brev-dev/another_esp8266_sensor_board/datasheets/microUSB_socket_2pin.jpg

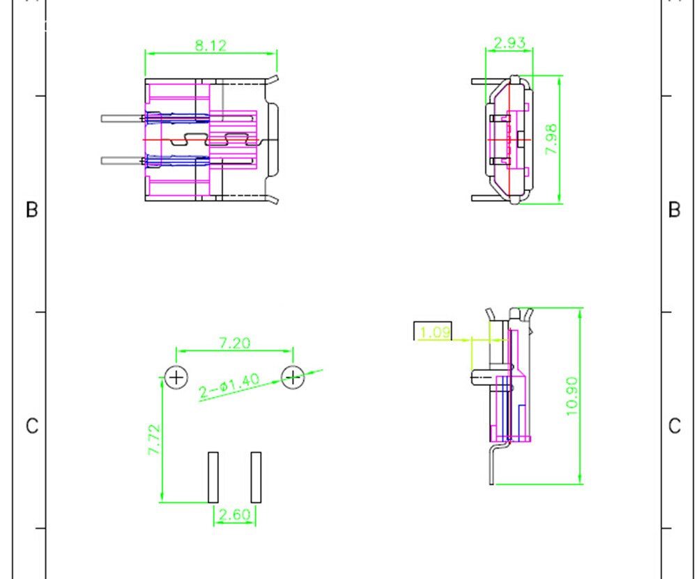
datasheets/microUSB_socket_2pin.jpg
