brev-dev/another_esp8266_sensor_board/datasheets/usbc_socket_6pin.webp

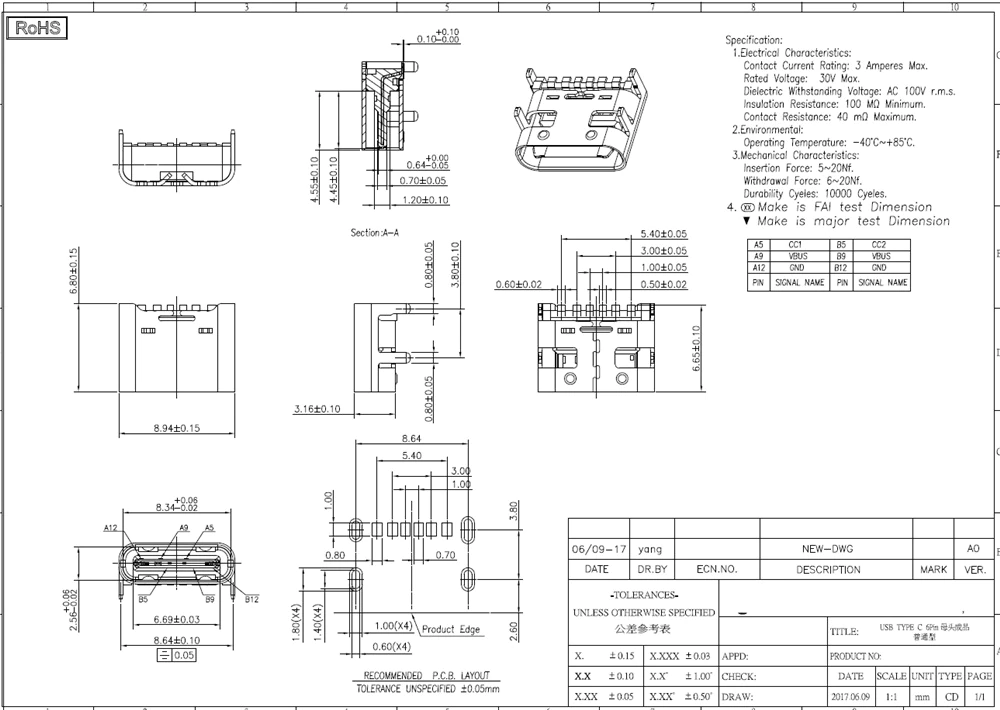
datasheets/usbc_socket_6pin.webp
