brev-dev/another_esp8266_sensor_board/images/antenna_bottom.jpg

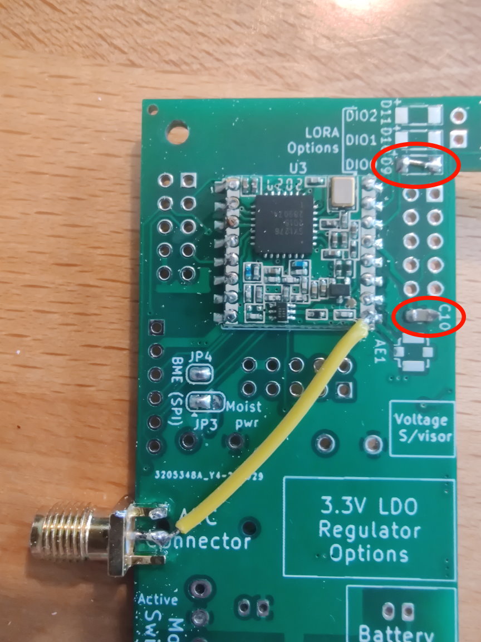
images/antenna_bottom.jpg
