brev-dev/another_esp8266_sensor_board/images/audio_socket_mod.jpg

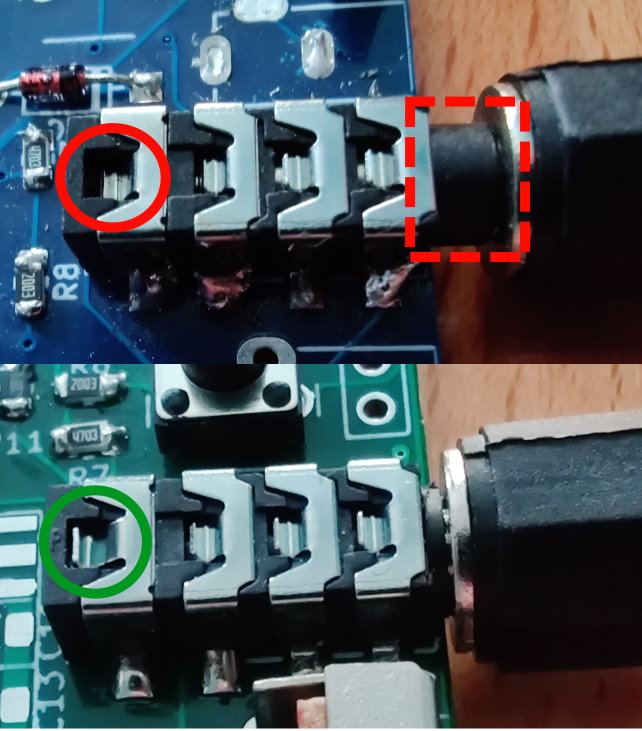
images/audio_socket_mod.jpg
