brev-dev/another_esp8266_sensor_board/images/bh1750_case.jpg

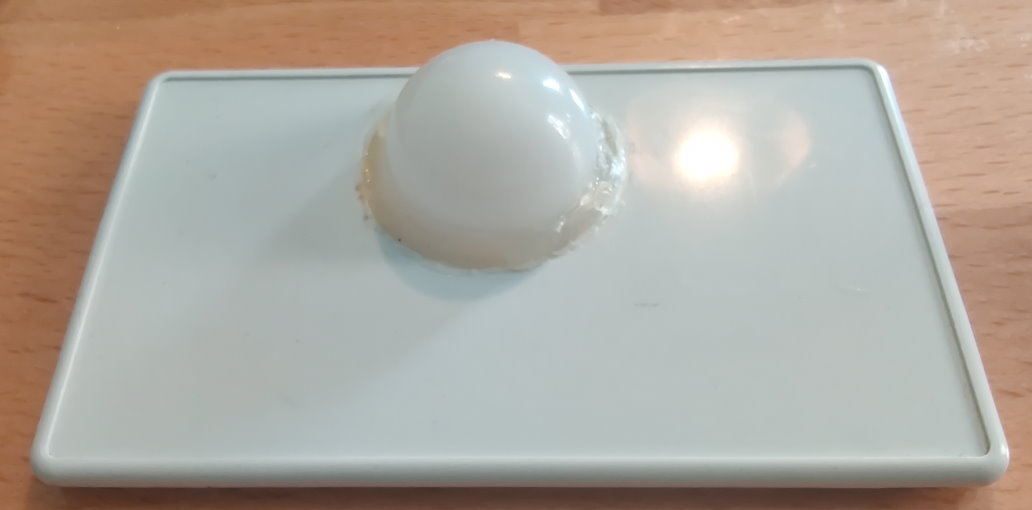
images/bh1750_case.jpg
