brev-dev/another_esp8266_sensor_board/images/bme280_trimmed_pins.jpg

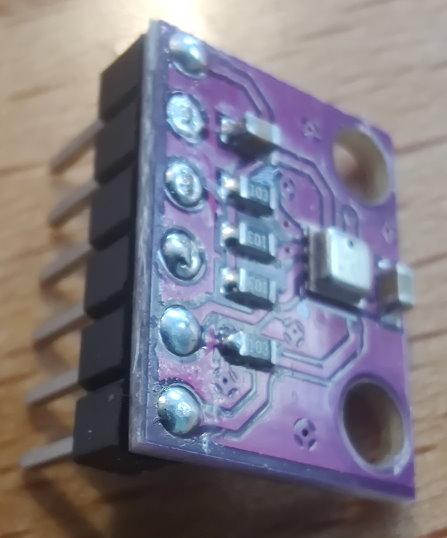
images/bme280_trimmed_pins.jpg
