brev-dev/another_esp8266_sensor_board/images/esp-12f programmer.jpg

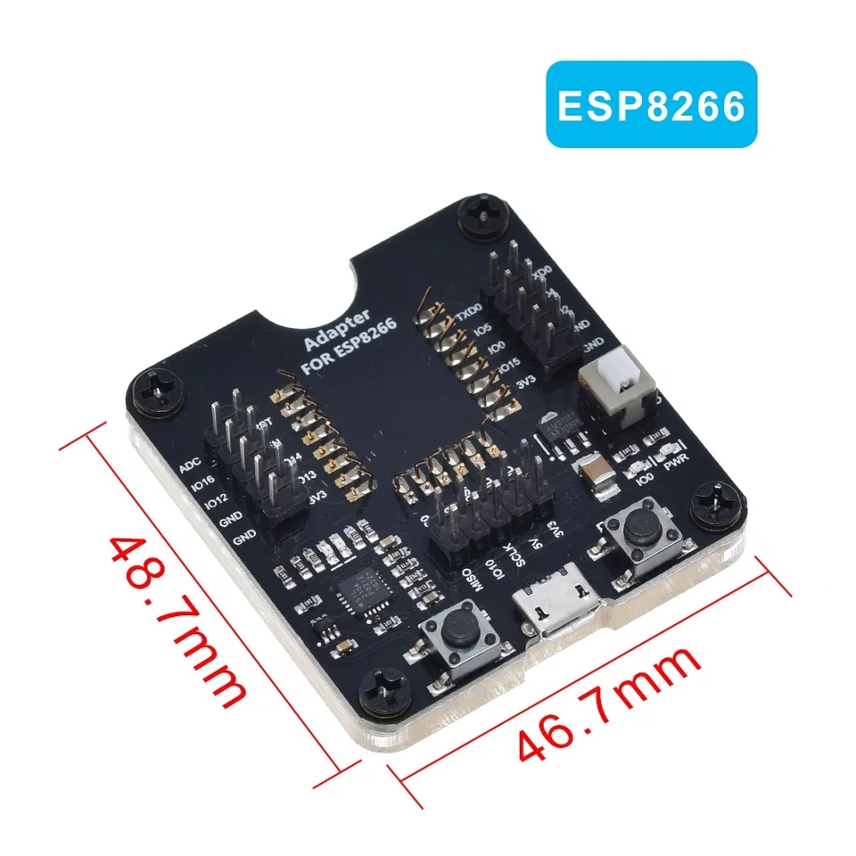
images/esp-12f programmer.jpg
