brev-dev/another_esp8266_sensor_board/images/me4056.jpg

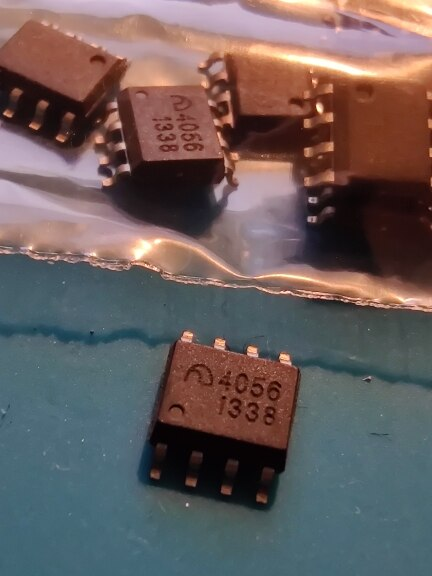
images/me4056.jpg
