brev-dev/another_esp8266_sensor_board/images/rear_solder_bridges_bme_spi.jpg

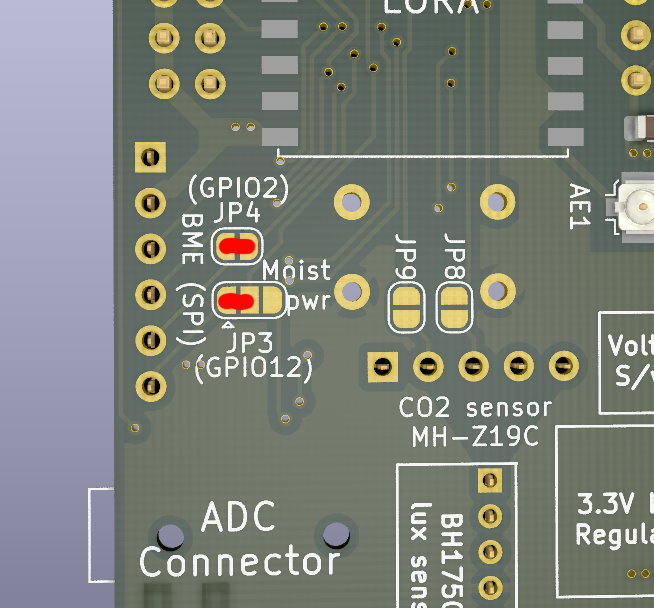
images/rear_solder_bridges_bme_spi.jpg
